0xkelvin/Keycap-Context/cad/renders/00-exploded.png

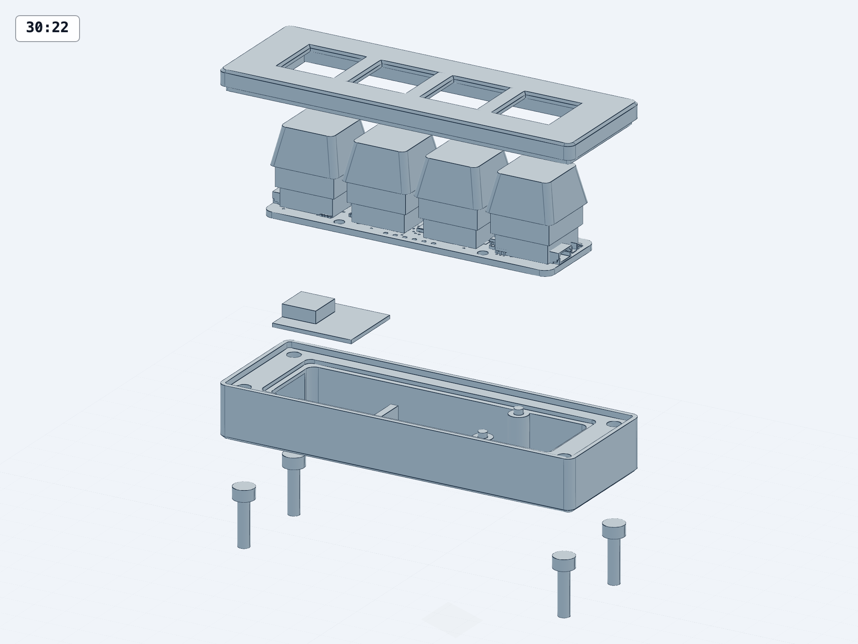
cad/renders/00-exploded.png
