0xkelvin/Keycap-Context/cad/renders/04-tray-internals.png

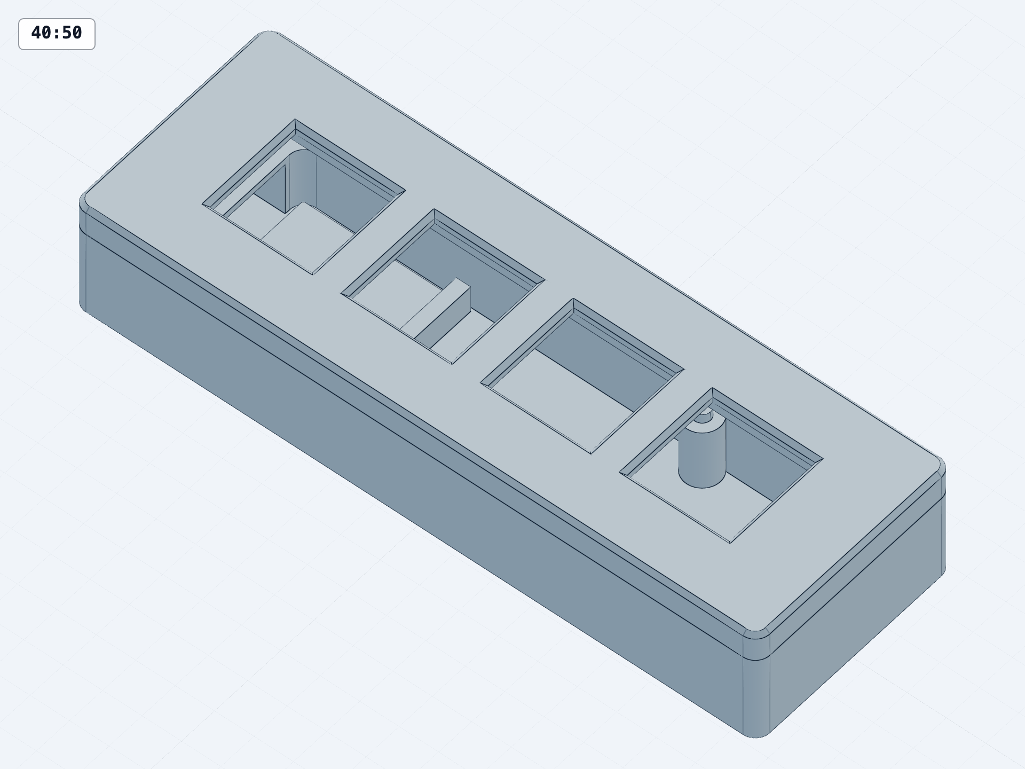
cad/renders/04-tray-internals.png
