0xkelvin/Keycap-Context/cad/renders/06-usb-end.png

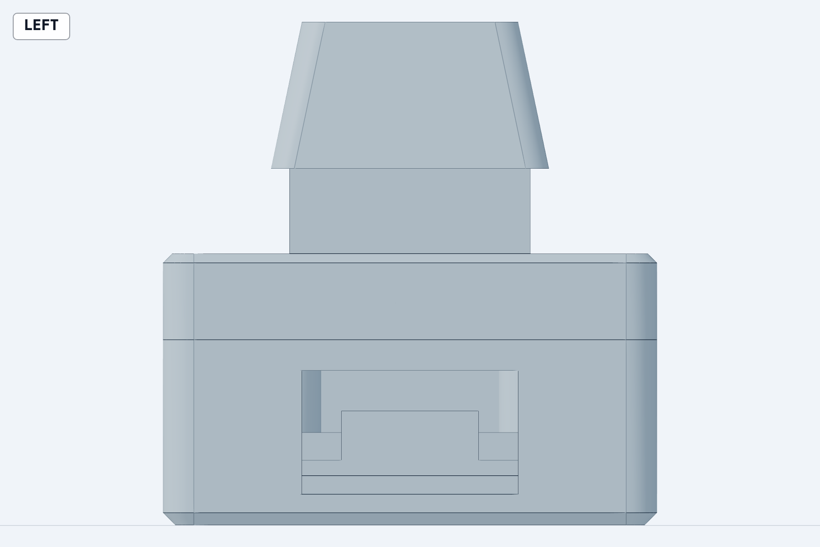
cad/renders/06-usb-end.png
