0xkelvin/Keycap-Context/cad/renders/08-cutaway-iso.png

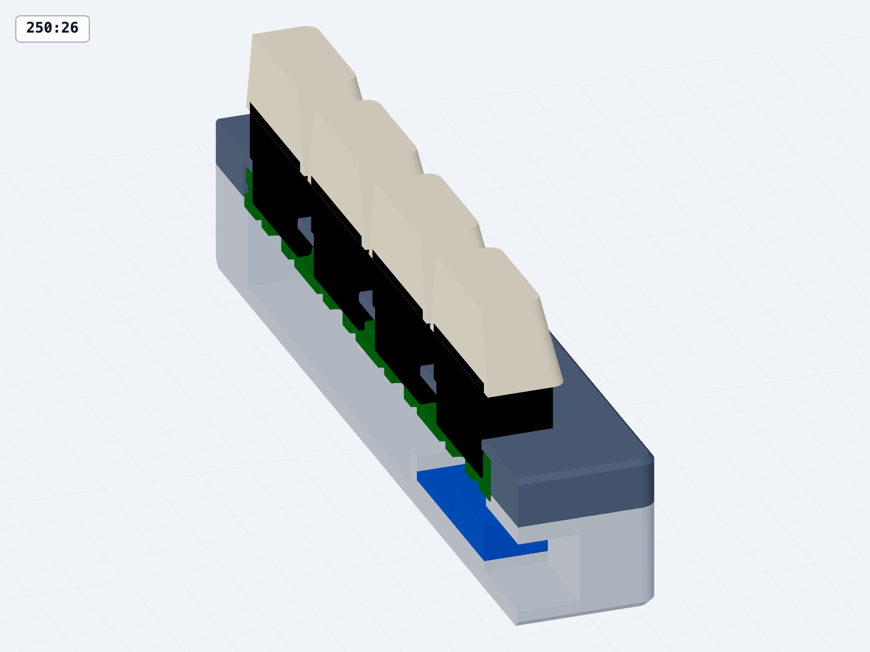
cad/renders/08-cutaway-iso.png
