0xkelvin/Keycap-Context/cad/renders/10-boards-in-tray-alt.png

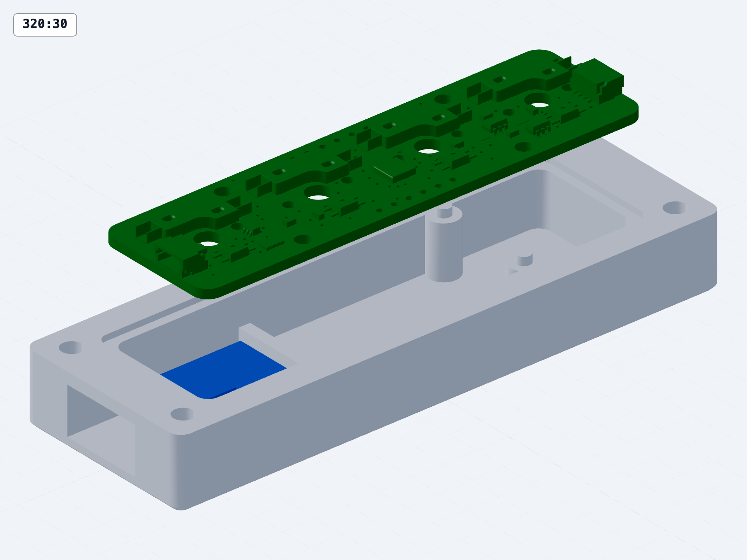
cad/renders/10-boards-in-tray-alt.png
