0xkelvin/Keycap-Context/cad/renders/12-xiao-retention.png

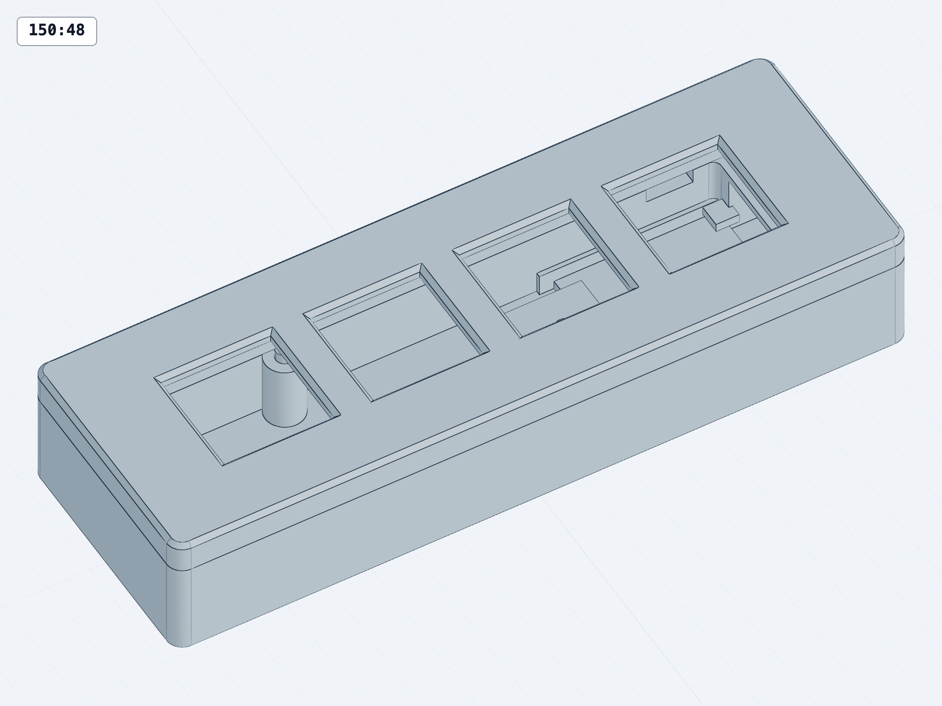
cad/renders/12-xiao-retention.png
