0xkelvin/Keycap-Context/cad/renders/colourways/bone.png

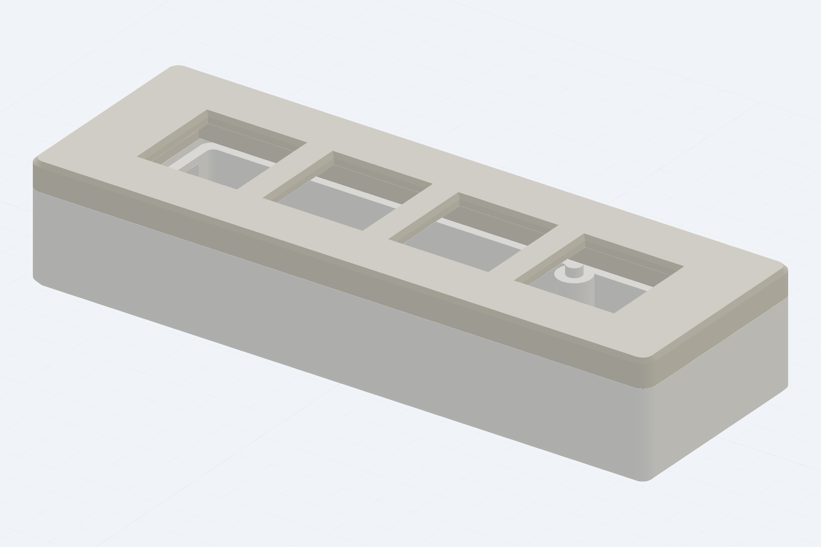
cad/renders/colourways/bone.png
