0xkelvin/Keycap-Context/cad/renders/colourways/graphite.png

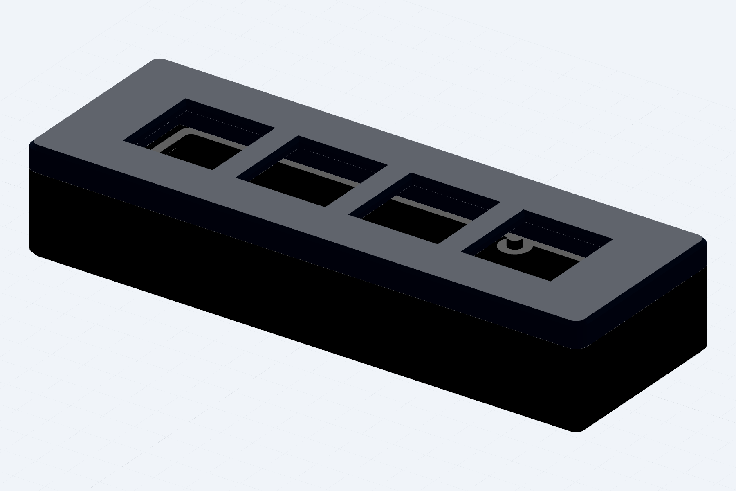
cad/renders/colourways/graphite.png
