0xkelvin/Keycap-Context/cad/renders/colourways/slate_sand.png

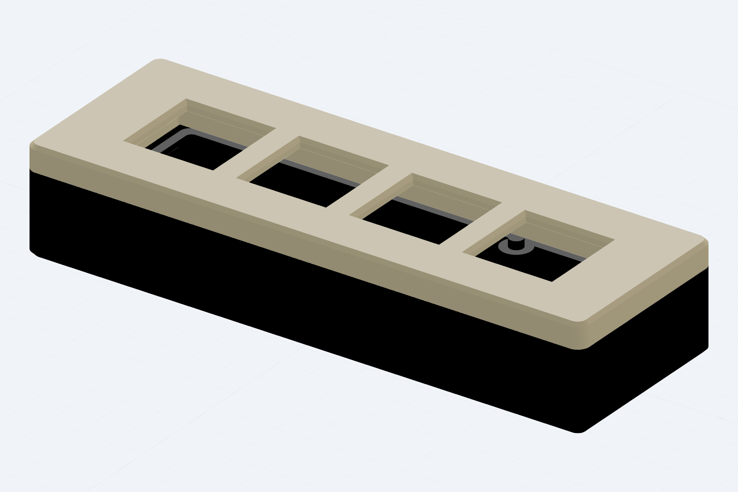
cad/renders/colourways/slate_sand.png
