0xkelvin/Keycap-Context/cad/renders/01-assembled-iso.png

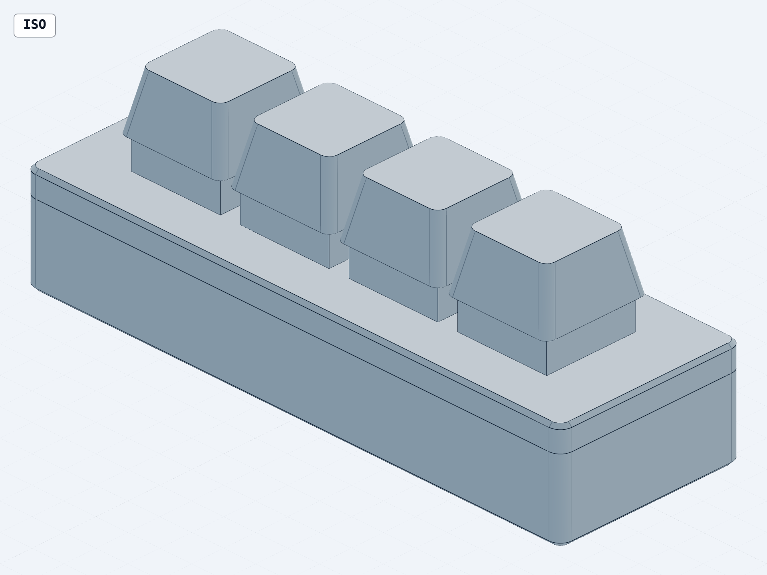
cad/renders/01-assembled-iso.png
