0xkelvin/Keycap-Context/cad/renders/02-assembled-top.png

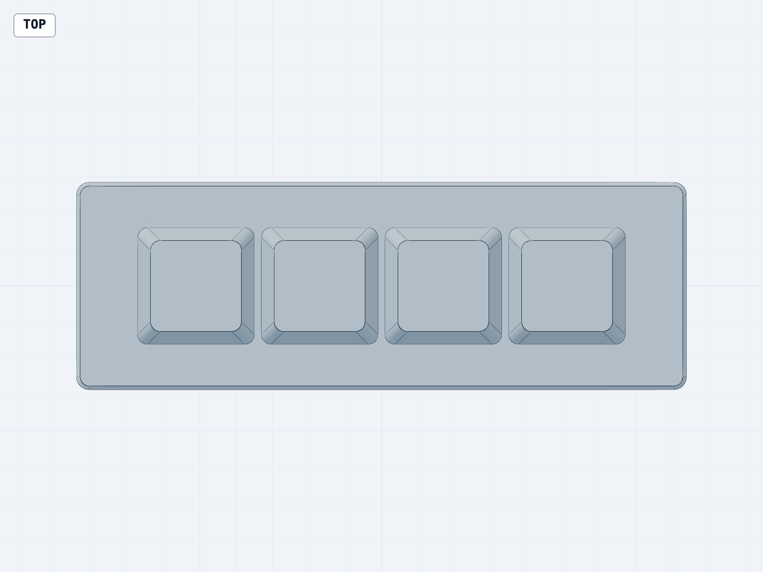
cad/renders/02-assembled-top.png
