0xkelvin/Keycap-Context/firmware/tests/protocol/src/main.c

/* SPDX-License-Identifier: Apache-2.0 */
#include "protocol.h"
#include "gesture.h"
#include "lighting.h"
#include "line_reader.h"
#include "audio_bands.h"

#include <string.h>
#include <zephyr/ztest.h>

ZTEST_SUITE(protocol, NULL, NULL, NULL, NULL, NULL);

ZTEST(protocol, test_ping)
{
	struct keycap_command command;
	zassert_true(keycap_protocol_parse("PING", &command), "PING should parse");
	zassert_equal(command.type, KEYCAP_COMMAND_PING, "wrong command type");
	zassert_true(keycap_protocol_parse("KEEPALIVE", &command),
		     "KEEPALIVE should parse");
	zassert_equal(command.type, KEYCAP_COMMAND_KEEPALIVE,
		      "wrong keepalive command type");
}

ZTEST(protocol, test_leds)
{
	struct keycap_command command;
	zassert_true(keycap_protocol_parse(
		"LEDS FF0000,00FF00,0000FF,102030", &command),
		"LEDS should parse");
	zassert_equal(command.leds[0].red, 255, "red component");
	zassert_equal(command.leds[1].green, 255, "green component");
	zassert_equal(command.leds[2].blue, 255, "blue component");
	zassert_equal(command.leds[3].green, 0x20, "mixed component");
}

ZTEST(protocol, test_rejects_bad_leds)
{
	struct keycap_command command;
	zassert_false(keycap_protocol_parse("LEDS FFFFFF", &command),
		      "must contain four colors");
	zassert_false(keycap_protocol_parse(
		"LEDS GG0000,00FF00,0000FF,102030", &command),
		"must contain hex colors");
}

ZTEST(protocol, test_button_format)
{
	char buffer[48];
	int length = keycap_protocol_format_button(buffer, sizeof(buffer), 4, true, 9);
	zassert_true(length > 0, "button event should format");
	zassert_equal(strcmp(buffer, "BUTTON 4 DOWN 9\n"), 0, "wrong event");
}

ZTEST(protocol, test_status)
{
	struct keycap_command command;
	zassert_true(keycap_protocol_parse("STATUS IDLE", &command),
		     "idle status should parse");
	zassert_true(keycap_protocol_parse("STATUS WAITING 3", &command),
		     "waiting status should parse");
	zassert_equal(command.type, KEYCAP_COMMAND_STATUS, "wrong command type");
	zassert_equal(command.active_choices, 3, "wrong active choice count");
	zassert_true(keycap_protocol_parse("STATUS WAITING 2 10A37F", &command),
		     "waiting status with accent should parse");
	zassert_true(command.has_status_color, "accent should be present");
	zassert_equal(command.status_color.green, 0xA3, "wrong accent color");
	zassert_false(keycap_protocol_parse("STATUS WAITING 5", &command),
		      "too many active choices must fail");
}

ZTEST(protocol, test_gesture_format)
{
	char buffer[48];
	zassert_true(keycap_protocol_format_gesture(buffer, sizeof(buffer), 2,
					     "DOUBLE", 11) > 0,
		     "gesture should format");
	zassert_equal(strcmp(buffer, "GESTURE 2 DOUBLE 11\n"), 0,
		      "wrong gesture event");
}

ZTEST(protocol, test_short_gesture_after_double_window)
{
	struct keycap_gesture_detector detector;
	struct keycap_gesture_event events[4];
	keycap_gesture_init(&detector);

	zassert_equal(keycap_gesture_update(&detector, 1, 0, events, 4), 0,
		      "press should wait");
	zassert_equal(keycap_gesture_update(&detector, 0, 80, events, 4), 0,
		      "release should wait for double press");
	zassert_equal(keycap_gesture_update(&detector, 0, 400, events, 4), 1,
		      "short press should emit after window");
	zassert_equal(events[0].type, KEYCAP_GESTURE_SHORT, "wrong gesture");
}

ZTEST(protocol, test_long_and_double_gestures)
{
	struct keycap_gesture_detector detector;
	struct keycap_gesture_event events[4];
	keycap_gesture_init(&detector);

	keycap_gesture_update(&detector, 1, 0, events, 4);
	zassert_equal(keycap_gesture_update(&detector, 1, 700, events, 4), 1,
		      "held key should emit long");
	zassert_equal(events[0].type, KEYCAP_GESTURE_LONG, "wrong long gesture");
	keycap_gesture_update(&detector, 0, 710, events, 4);

	keycap_gesture_init(&detector);
	keycap_gesture_update(&detector, 2, 0, events, 4);
	keycap_gesture_update(&detector, 0, 60, events, 4);
	keycap_gesture_update(&detector, 2, 160, events, 4);
	zassert_equal(keycap_gesture_update(&detector, 0, 220, events, 4), 1,
		      "second release should emit double");
	zassert_equal(events[0].type, KEYCAP_GESTURE_DOUBLE, "wrong double gesture");
}

ZTEST(protocol, test_pressed_keys_use_distinct_solid_colors)
{
	struct keycap_rgb colors[KEYCAP_LED_COUNT];
	struct keycap_lighting_profile profile;
	keycap_lighting_default(&profile);

	keycap_lighting_render(&profile, BIT(0), 0, colors);
	zassert_equal(colors[0].red, 0, "button 1 red component");
	zassert_equal(colors[0].green, 178, "button 1 should be brightness-scaled green");
	zassert_equal(colors[0].blue, 22, "button 1 blue component");
	zassert_equal(colors[1].red | colors[1].green | colors[1].blue, 0,
		      "unpressed button should be off");

	keycap_lighting_render(&profile, BIT(1) | BIT(3), 0, colors);
	zassert_equal(colors[1].blue, 178, "button 2 should be brightness-scaled blue");
	zassert_equal(colors[3].red, 178, "button 4 should be brightness-scaled orange");
	zassert_equal(colors[2].red | colors[2].green | colors[2].blue, 0,
		      "unpressed button should remain off");
}

ZTEST(protocol, test_idle_rainbow_animates_all_four_keys)
{
	struct keycap_rgb first[KEYCAP_LED_COUNT];
	struct keycap_rgb next[KEYCAP_LED_COUNT];
	struct keycap_lighting_profile profile;
	keycap_lighting_default(&profile);

	keycap_lighting_render(&profile, 0, 0, first);
	keycap_lighting_render(&profile, 0, 1200 / profile.speed, next);

	for (uint8_t index = 0; index < KEYCAP_LED_COUNT; ++index) {
		zassert_not_equal(first[index].red | first[index].green | first[index].blue,
				  0, "idle key %u should be illuminated", index + 1);
	}
	zassert_not_equal(memcmp(first, next, sizeof(first)), 0,
			  "rainbow should advance each frame");
}

ZTEST(protocol, test_lighting_profile_command)
{
	struct keycap_command command;
	zassert_true(keycap_protocol_parse(
		"LIGHTING BREATHING 70 50 00FF20,0070FF,DC00FF,FF4800", &command),
		"installed breathing profile should parse");
	zassert_true(keycap_protocol_parse(
		"LIGHTING REACTIVE 80 65 00FF20,0070FF,DC00FF,FF4800", &command),
		"valid lighting profile should parse");
	zassert_equal(command.type, KEYCAP_COMMAND_LIGHTING, "wrong command type");
	zassert_equal(command.lighting.mode, KEYCAP_LIGHTING_REACTIVE, "wrong mode");
	zassert_equal(command.lighting.brightness, 80, "wrong brightness");
	zassert_equal(command.lighting.speed, 65, "wrong speed");
	zassert_equal(command.lighting.key_colors[1].blue, 255, "wrong key color");
	zassert_false(keycap_protocol_parse(
		"LIGHTING RAINBOW 101 50 00FF20,0070FF,DC00FF,FF4800", &command),
		"brightness over 100 should fail");
}

ZTEST(protocol, test_agent_status_command)
{
	struct keycap_command command;
	zassert_true(keycap_protocol_parse(
		"AGENTS WORKING,EMPTY,EMPTY,EMPTY", &command),
		"installed agent state should parse");
	zassert_true(keycap_protocol_parse(
		"AGENTS WORKING,WAITING,DONE,ERROR", &command),
		"agent command should parse");
	zassert_equal(command.type, KEYCAP_COMMAND_AGENTS, "wrong command type");
	zassert_equal(command.agents[0], KEYCAP_AGENT_WORKING, "wrong first state");
	zassert_equal(command.agents[1], KEYCAP_AGENT_WAITING, "wrong second state");
	zassert_equal(command.agents[2], KEYCAP_AGENT_DONE, "wrong third state");
	zassert_equal(command.agents[3], KEYCAP_AGENT_ERROR, "wrong fourth state");
	zassert_false(keycap_protocol_parse("AGENTS WORKING,WAITING,DONE", &command),
		      "agent command must contain four states");
}

ZTEST(protocol, test_agent_status_render)
{
	enum keycap_agent_state states[KEYCAP_LED_COUNT] = {
		KEYCAP_AGENT_WORKING, KEYCAP_AGENT_WAITING,
		KEYCAP_AGENT_DONE, KEYCAP_AGENT_ERROR,
	};
	struct keycap_rgb colors[KEYCAP_LED_COUNT];
	keycap_agent_render(states, 0, 1000, colors);
	zassert_true(colors[0].blue > 0, "working state should be blue");
	zassert_true(colors[1].red > 0 && colors[1].green > 0,
		     "waiting state should be orange");
	zassert_true(colors[2].green > colors[2].red,
		     "done state should be green");
	zassert_true(colors[3].red > 0 && colors[3].green == 0,
		     "error state should be red");
}


static enum keycap_line_status push_text(struct keycap_line_reader *reader,
					 const char *text)
{
	enum keycap_line_status status = KEYCAP_LINE_NONE;

	for (const char *cursor = text; *cursor != '\0'; ++cursor) {
		status = keycap_line_reader_push(reader, (uint8_t)*cursor);
	}
	return status;
}

ZTEST(protocol, test_line_reader_frames_commands)
{
	struct keycap_line_reader reader;

	keycap_line_reader_init(&reader);
	zassert_equal(push_text(&reader, "PING\n"), KEYCAP_LINE_READY,
		      "a terminated command should be ready");
	zassert_str_equal(reader.line, "PING", "unexpected command text");

	/* Carriage returns and empty lines must not produce commands. */
	zassert_equal(push_text(&reader, "\r\n"), KEYCAP_LINE_NONE,
		      "an empty line is not a command");
	zassert_equal(push_text(&reader, "STATUS IDLE\r\n"), KEYCAP_LINE_READY,
		      "CRLF should terminate a command");
	zassert_str_equal(reader.line, "STATUS IDLE", "CR must be stripped");
}

ZTEST(protocol, test_line_reader_resynchronizes_after_dropped_bytes)
{
	struct keycap_line_reader reader;

	keycap_line_reader_init(&reader);
	/* "PING\nPING\n" with the first newline dropped by a full receive ring
	 * previously spliced into the unparsable command "PIPING".
	 */
	zassert_equal(push_text(&reader, "PI"), KEYCAP_LINE_NONE, "partial line");
	keycap_line_reader_resynchronize(&reader);
	zassert_equal(push_text(&reader, "PING"), KEYCAP_LINE_NONE,
		      "the damaged remainder must be discarded");
	zassert_equal(push_text(&reader, "\n"), KEYCAP_LINE_NONE,
		      "the newline only ends the discarded region");
	zassert_equal(push_text(&reader, "KEEPALIVE\n"), KEYCAP_LINE_READY,
		      "the next whole command must be delivered");
	zassert_str_equal(reader.line, "KEEPALIVE", "unexpected command text");
}

ZTEST(protocol, test_line_reader_discards_overlong_command_tail)
{
	struct keycap_line_reader reader;
	char overlong[KEYCAP_LINE_MAX + 8];

	keycap_line_reader_init(&reader);
	memset(overlong, 'A', sizeof(overlong) - 1);
	overlong[sizeof(overlong) - 1] = '\0';
	zassert_equal(push_text(&reader, overlong), KEYCAP_LINE_NONE,
		      "only the first overflowing byte reports overflow");

	keycap_line_reader_init(&reader);
	memset(overlong, 'A', KEYCAP_LINE_MAX);
	overlong[KEYCAP_LINE_MAX] = '\0';
	zassert_equal(push_text(&reader, overlong), KEYCAP_LINE_OVERFLOW,
		      "exceeding the buffer must report overflow");
	/* The tail must not be parsed as a second command. */
	zassert_equal(push_text(&reader, "BBB\nPING\n"), KEYCAP_LINE_READY,
		      "framing resumes at the next newline");
	zassert_str_equal(reader.line, "PING", "the tail must be discarded");
}

/* Fill a frame with a square wave of the given period, in samples. */
static void make_tone(int16_t *samples, size_t count, size_t period, int16_t amplitude)
{
	for (size_t i = 0; i < count; ++i) {
		samples[i] = ((i / (period / 2u)) % 2u) ? amplitude : (int16_t)-amplitude;
	}
}

ZTEST(protocol, test_audio_rejects_dc_offset)
{
	struct keycap_audio_filters filters;
	struct keycap_audio_energy energy;
	int16_t samples[256];

	keycap_audio_filters_reset(&filters);
	for (size_t i = 0; i < ARRAY_SIZE(samples); ++i) {
		samples[i] = 6000;
	}
	/* The PDM stream carries a DC offset; left in place it reads as a
	 * constant loud signal and holds the display open on silence.
	 */
	for (int pass = 0; pass < 40; ++pass) {
		keycap_audio_filters_run(&filters, samples, ARRAY_SIZE(samples), &energy);
	}
	zassert_true(energy.overall < 40u, "steady DC is not sound");
	zassert_true(energy.band[0] < 200u, "and must not register as bass");
}

ZTEST(protocol, test_audio_measures_amplitude)
{
	struct keycap_audio_filters filters;
	struct keycap_audio_energy energy;
	int16_t samples[256];

	keycap_audio_filters_reset(&filters);
	make_tone(samples, ARRAY_SIZE(samples), 64, 8000);
	for (int pass = 0; pass < 8; ++pass) {
		keycap_audio_filters_run(&filters, samples, ARRAY_SIZE(samples), &energy);
	}
	zassert_true(energy.overall > 7000u && energy.overall < 9000u,
		     "overall energy should track mean absolute amplitude");
}

ZTEST(protocol, test_audio_separates_low_and_high_bands)
{
	struct keycap_audio_filters filters;
	struct keycap_audio_energy low;
	struct keycap_audio_energy high;
	int16_t samples[256];

	/* 125 Hz at 16 kHz: squarely in the bass band. */
	keycap_audio_filters_reset(&filters);
	make_tone(samples, ARRAY_SIZE(samples), 128, 8000);
	for (int pass = 0; pass < 8; ++pass) {
		keycap_audio_filters_run(&filters, samples, ARRAY_SIZE(samples), &low);
	}

	/* Alternating every sample is 8 kHz, the top of the range. */
	keycap_audio_filters_reset(&filters);
	make_tone(samples, ARRAY_SIZE(samples), 2, 8000);
	for (int pass = 0; pass < 8; ++pass) {
		keycap_audio_filters_run(&filters, samples, ARRAY_SIZE(samples), &high);
	}

	zassert_true(low.band[0] > low.band[3], "a low tone belongs to the bass key");
	zassert_true(high.band[3] > high.band[0], "a high tone belongs to the treble key");
}

ZTEST(protocol, test_audio_bands_normalise_independently)
{
	struct keycap_audio_analyzer analyzer;
	struct keycap_audio_energy energy = {0};

	/* The spectrum moves each key on its own band, unlike the meter's bar. */
	keycap_audio_analyzer_init(&analyzer);
	for (int i = 0; i < 40; ++i) {
		energy.overall = 30u;
		energy.band[0] = 30u;
		energy.band[3] = 30u;
		keycap_audio_analyzer_update(&analyzer, &energy);
	}
	for (int i = 0; i < 30; ++i) {
		energy.overall = 4000u;
		energy.band[0] = 4000u;
		energy.band[3] = 30u;
		keycap_audio_analyzer_update(&analyzer, &energy);
	}
	zassert_true(keycap_audio_analyzer_band(&analyzer, 0) > 200u,
		     "a loud bass band should light its own key");
	zassert_equal(keycap_audio_analyzer_band(&analyzer, 3), 0,
		      "a silent treble band should leave its key dark");
}

ZTEST(protocol, test_audio_fills_the_keys_as_one_bar)
{
	/* Each key completes before the next begins: louder sound lights more
	 * keys, never different ones.
	 */
	zassert_equal(keycap_audio_key_fill(0, 0), 0, "silence leaves the bar empty");
	zassert_equal(keycap_audio_key_fill(64, 0), 255, "a quarter fills the first key");
	zassert_equal(keycap_audio_key_fill(128, 1), 255, "a half fills the second key");
	zassert_equal(keycap_audio_key_fill(255, 3), 255, "peak fills every key");

	for (uint16_t level = 0; level <= 255u; ++level) {
		for (uint8_t key = 1; key < KEYCAP_LED_COUNT; ++key) {
			if (keycap_audio_key_fill((uint8_t)level, key) > 0u) {
				zassert_equal(
					keycap_audio_key_fill((uint8_t)level, key - 1u), 255,
					"a key may only light once the one below is full");
			}
		}
	}
}

ZTEST(protocol, test_audio_normalises_against_its_own_range)
{
	struct keycap_audio_analyzer analyzer;

	struct keycap_audio_energy energy = {0};

	keycap_audio_analyzer_init(&analyzer);
	for (int i = 0; i < 60; ++i) {
		energy.overall = 20u;
		keycap_audio_analyzer_update(&analyzer, &energy);
	}
	zassert_equal(keycap_audio_analyzer_level(&analyzer), 0,
		      "room noise must not drive the meter");

	for (int i = 0; i < 30; ++i) {
		energy.overall = 6000u;
		keycap_audio_analyzer_update(&analyzer, &energy);
	}
	zassert_true(keycap_audio_analyzer_level(&analyzer) > 220u,
		     "music should reach the top of the bar");
}

ZTEST(protocol, test_audio_release_is_eased_not_instant)
{
	struct keycap_audio_analyzer analyzer;

	struct keycap_audio_energy energy = {0};

	keycap_audio_analyzer_init(&analyzer);
	for (int i = 0; i < 30; ++i) {
		energy.overall = 6000u;
		keycap_audio_analyzer_update(&analyzer, &energy);
	}
	uint8_t peak = keycap_audio_analyzer_level(&analyzer);

	energy.overall = 30u;
	keycap_audio_analyzer_update(&analyzer, &energy);
	uint8_t after = keycap_audio_analyzer_level(&analyzer);
	zassert_true(after < peak, "the meter must fall");
	zassert_true(after > peak / 2u, "but not collapse in a single frame");
}

/* Run the analyser until its channels settle, then read the hue. */
static uint8_t settle_pitch(struct keycap_audio_analyzer *analyzer, uint32_t low,
			    uint32_t low_mid, uint32_t high_mid, uint32_t high,
			    int frames)
{
	struct keycap_audio_energy energy = {0};

	for (int i = 0; i < frames; ++i) {
		energy.overall = (low + low_mid + high_mid + high) / 4u;
		energy.band[0] = low;
		energy.band[1] = low_mid;
		energy.band[2] = high_mid;
		energy.band[3] = high;
		keycap_audio_analyzer_update(analyzer, &energy);
	}
	return keycap_audio_analyzer_pitch(analyzer);
}

ZTEST(protocol, test_pitch_colour_follows_the_spectrum)
{
	struct keycap_audio_analyzer analyzer;

	keycap_audio_analyzer_init(&analyzer);
	settle_pitch(&analyzer, 500, 500, 500, 500, 60);
	uint8_t bass = settle_pitch(&analyzer, 9000, 400, 300, 200, 120);

	keycap_audio_analyzer_init(&analyzer);
	settle_pitch(&analyzer, 500, 500, 500, 500, 60);
	uint8_t mid = settle_pitch(&analyzer, 300, 9000, 8000, 300, 120);

	keycap_audio_analyzer_init(&analyzer);
	settle_pitch(&analyzer, 500, 500, 500, 500, 60);
	uint8_t treble = settle_pitch(&analyzer, 200, 300, 400, 9000, 120);

	/* Red through green to violet as the energy climbs the spectrum. */
	zassert_true(bass < mid, "bass should sit warmer than mids");
	zassert_true(mid < treble, "treble should sit cooler than mids");
	zassert_true(bass < 45u, "bass belongs at the red end, not merely warm");
	zassert_true(treble > 140u, "treble belongs at the violet end");
}

ZTEST(protocol, test_pitch_colour_holds_through_silence)
{
	struct keycap_audio_analyzer analyzer;

	keycap_audio_analyzer_init(&analyzer);
	settle_pitch(&analyzer, 200, 300, 400, 9000, 120);
	uint8_t before = keycap_audio_analyzer_pitch(&analyzer);

	/* Silence carries no spectrum, so the colour must hold rather than snap
	 * back to red between tracks.
	 */
	uint8_t after = settle_pitch(&analyzer, 0, 0, 0, 0, 40);
	zassert_equal(after, before, "silence must not reset the hue");
}

static void feed_overall(struct keycap_audio_analyzer *analyzer, uint32_t level,
			 uint32_t frames)
{
	struct keycap_audio_energy energy = {0};

	for (uint32_t i = 0; i < frames; ++i) {
		energy.overall = level;
		energy.band[0] = level;
		energy.band[1] = level / 2u;
		energy.band[2] = level / 3u;
		energy.band[3] = level / 4u;
		keycap_audio_analyzer_update(analyzer, &energy);
	}
}

ZTEST(protocol, test_microphone_sleeps_only_after_real_silence)
{
	struct keycap_audio_analyzer analyzer;

	/* Music keeps its peak far above its floor, so it never sleeps however
	 * long it plays.
	 */
	keycap_audio_analyzer_init(&analyzer);
	for (int i = 0; i < 400; ++i) {
		feed_overall(&analyzer, 6000u, 3u);
		feed_overall(&analyzer, 200u, 3u);
	}
	zassert_false(keycap_audio_analyzer_is_quiet(&analyzer),
		      "music must not put the microphone to sleep");

	/* A gap between tracks is not silence either. */
	keycap_audio_analyzer_init(&analyzer);
	feed_overall(&analyzer, 6000u, 60u);
	feed_overall(&analyzer, 200u, KEYCAP_AUDIO_SLEEP_FRAMES / 4u);
	zassert_false(keycap_audio_analyzer_is_quiet(&analyzer),
		      "a short gap must not sleep the microphone");

	/* A room's own noise has almost no dynamic range: sleep. The peak needs
	 * a few hundred frames to decay before the countdown starts.
	 */
	feed_overall(&analyzer, 200u, KEYCAP_AUDIO_SLEEP_FRAMES + 1000u);
	zassert_true(keycap_audio_analyzer_is_quiet(&analyzer),
		     "sustained silence should release the microphone");

	/* And sound returning revives it immediately. */
	feed_overall(&analyzer, 6000u, 5u);
	zassert_false(keycap_audio_analyzer_is_quiet(&analyzer),
		      "sound must reset the countdown at once");
}

static void play_beats(struct keycap_audio_analyzer *analyzer, int kicks, int gap)
{
	struct keycap_audio_energy energy = {0};

	for (int kick = 0; kick < kicks; ++kick) {
		for (int i = 0; i < 3; ++i) {
			energy.overall = 9000u; energy.band[0] = 9000u;
			energy.band[1] = 800u; energy.band[2] = 600u; energy.band[3] = 400u;
			keycap_audio_analyzer_update(analyzer, &energy);
		}
		for (int i = 0; i < gap; ++i) {
			energy.overall = 1200u; energy.band[0] = 1200u;
			energy.band[1] = 800u; energy.band[2] = 600u; energy.band[3] = 400u;
			keycap_audio_analyzer_update(analyzer, &energy);
		}
	}
}

ZTEST(protocol, test_beats_count_transients_not_loudness)
{
	struct keycap_audio_analyzer analyzer;
	struct keycap_audio_energy energy = {0};

	keycap_audio_analyzer_init(&analyzer);
	play_beats(&analyzer, 1, 60);
	uint32_t before = keycap_audio_analyzer_beats(&analyzer);
	play_beats(&analyzer, 16, 25);
	uint32_t counted = keycap_audio_analyzer_beats(&analyzer) - before;
	zassert_true(counted >= 12u && counted <= 16u,
		     "a steady kick should be counted once each");

	/* A sustained bass note sits above its own average for as long as it
	 * lasts, so loudness alone must not count as a beat.
	 */
	keycap_audio_analyzer_init(&analyzer);
	for (int i = 0; i < 600; ++i) {
		energy.overall = 4000u; energy.band[0] = 4000u;
		energy.band[1] = 800u; energy.band[2] = 600u; energy.band[3] = 400u;
		keycap_audio_analyzer_update(&analyzer, &energy);
	}
	zassert_equal(keycap_audio_analyzer_beats(&analyzer), 0,
		      "a held bass note is not a run of beats");

	keycap_audio_analyzer_init(&analyzer);
	for (int i = 0; i < 600; ++i) {
		memset(&energy, 0, sizeof(energy));
		keycap_audio_analyzer_update(&analyzer, &energy);
	}
	zassert_equal(keycap_audio_analyzer_beats(&analyzer), 0, "silence has no beats");
}

ZTEST(protocol, test_analyzer_init_clears_every_field)
{
	struct keycap_audio_analyzer analyzer;

	/* The analyzer lives on the audio thread's stack, so a partial
	 * initialiser leaves beats, pitch and the quiet countdown holding
	 * whatever was there before.
	 */
	memset(&analyzer, 0xa5, sizeof(analyzer));
	keycap_audio_analyzer_init(&analyzer);

	zassert_equal(keycap_audio_analyzer_beats(&analyzer), 0, "beats");
	zassert_equal(keycap_audio_analyzer_pitch(&analyzer), 0, "pitch");
	zassert_equal(keycap_audio_analyzer_level(&analyzer), 0, "level");
	zassert_false(keycap_audio_analyzer_is_quiet(&analyzer), "quiet countdown");
}
